mkulesh/stm32DevelopmentBoards/images/boards_bottom_view.jpg

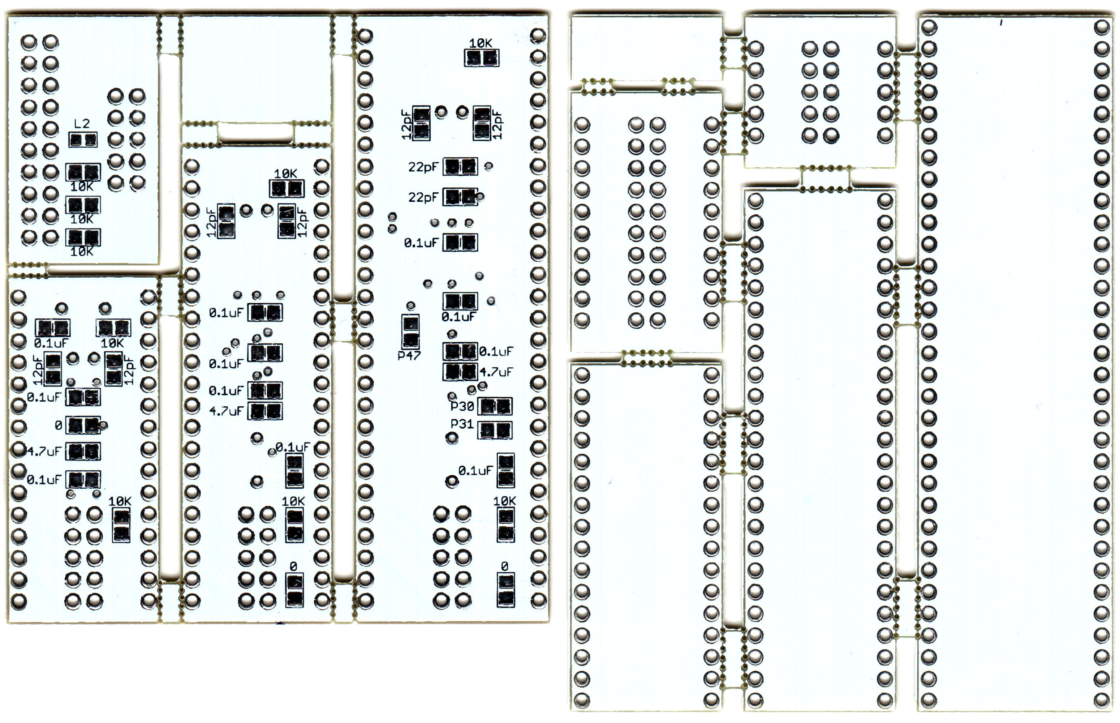
images/boards_bottom_view.jpg
