mkulesh/stm32DevelopmentBoards/images/boards_top_view.jpg

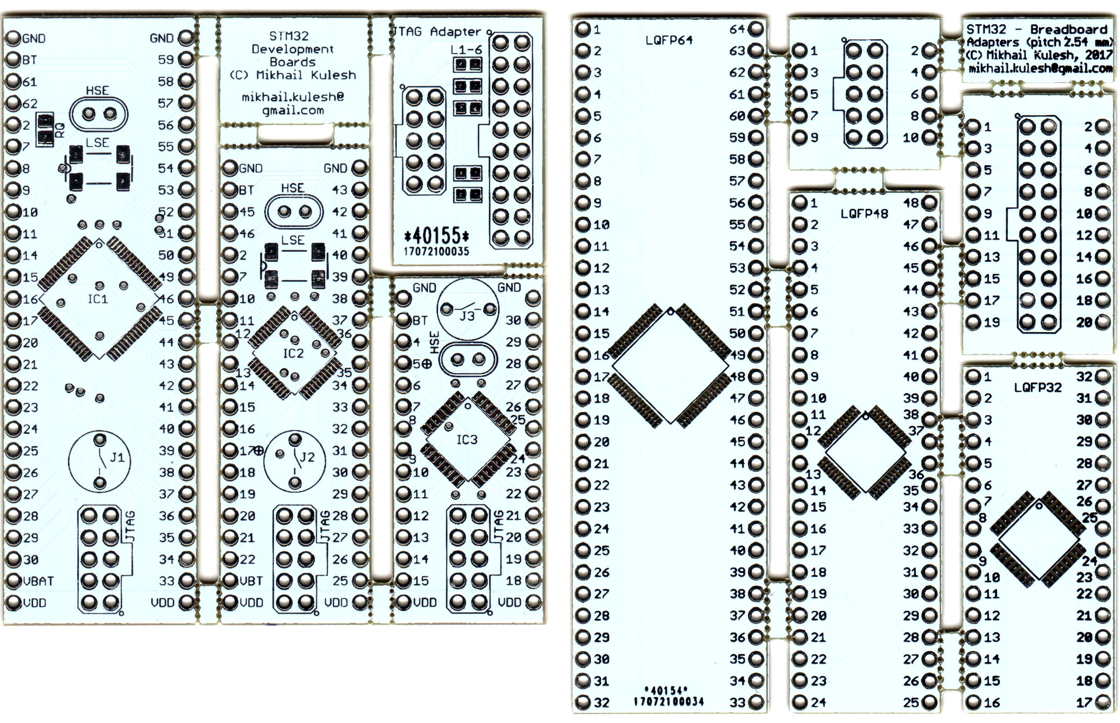
images/boards_top_view.jpg
