mkulesh/stm32DevelopmentBoards/images/F303K8_dev_board_jtag.jpg

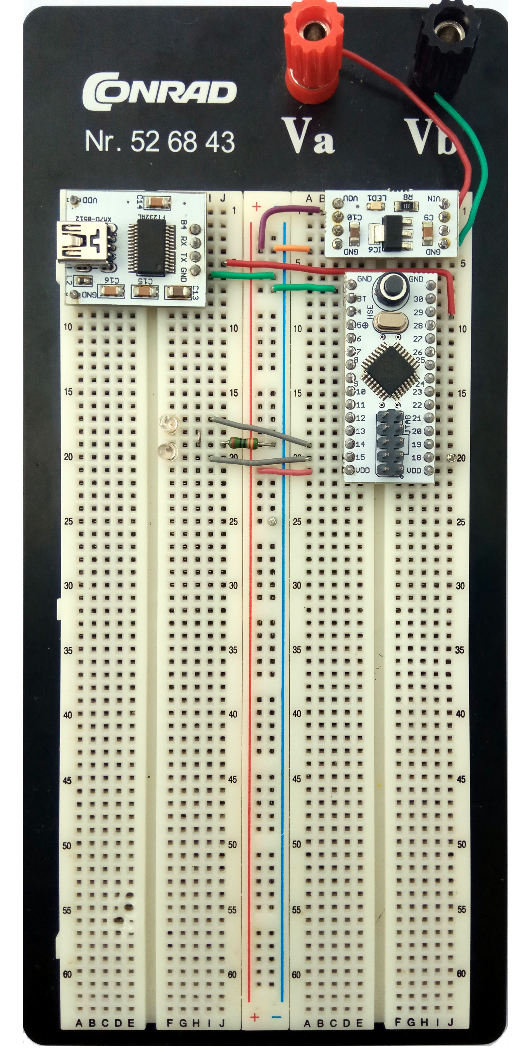
images/F303K8_dev_board_jtag.jpg
