mkulesh/stm32DevelopmentBoards/images/F373CB_adapter_board_jtag.jpg

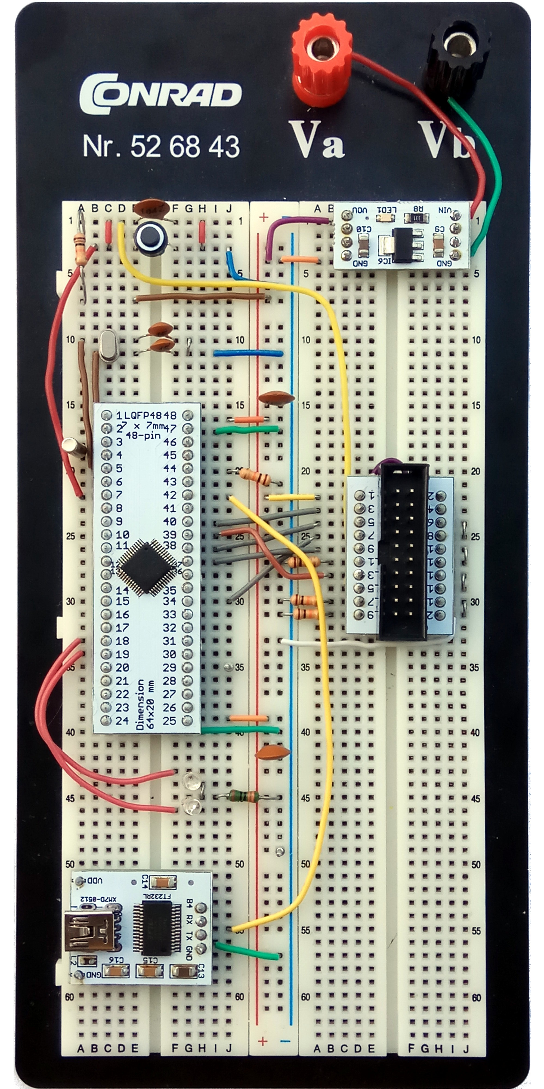
images/F373CB_adapter_board_jtag.jpg
