mkulesh/stm32DevelopmentBoards/images/F410RB_adapter_board_jtag.jpg

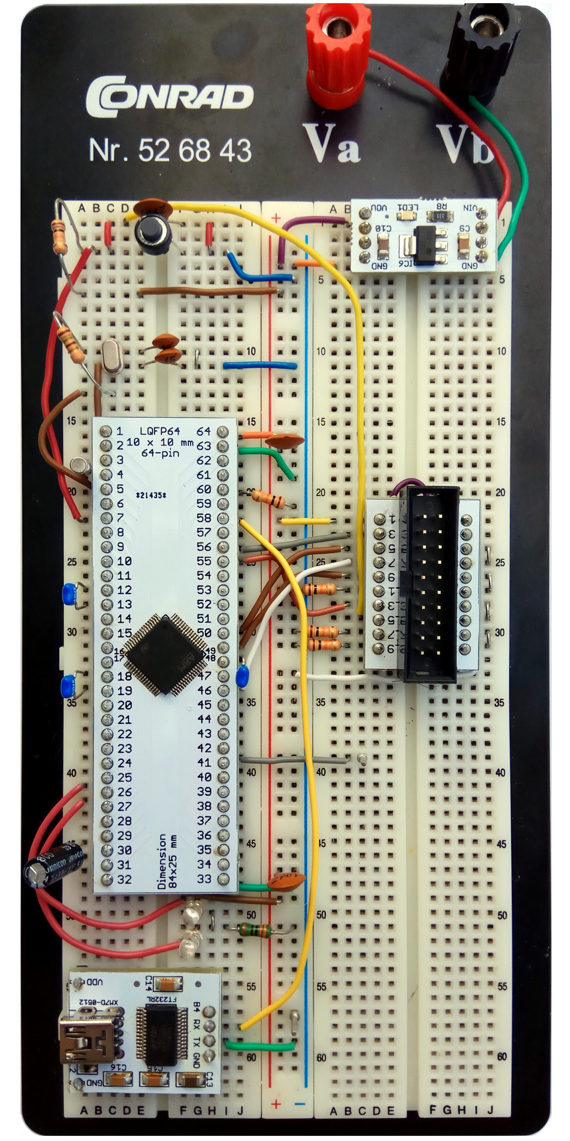
images/F410RB_adapter_board_jtag.jpg
