mkulesh/stm32DevelopmentBoards/images/F410RB_dev_board_jtag.jpg

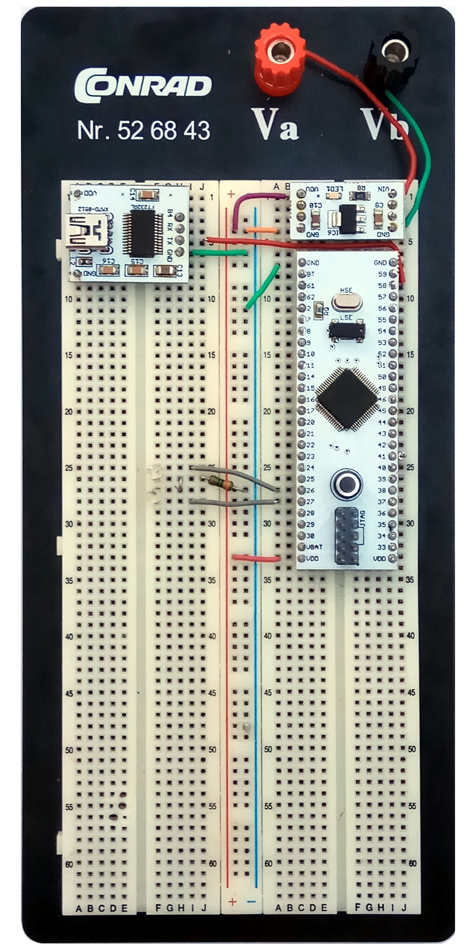
images/F410RB_dev_board_jtag.jpg
