mkulesh/stm32DevelopmentBoards/images/stm32pi-case.jpg

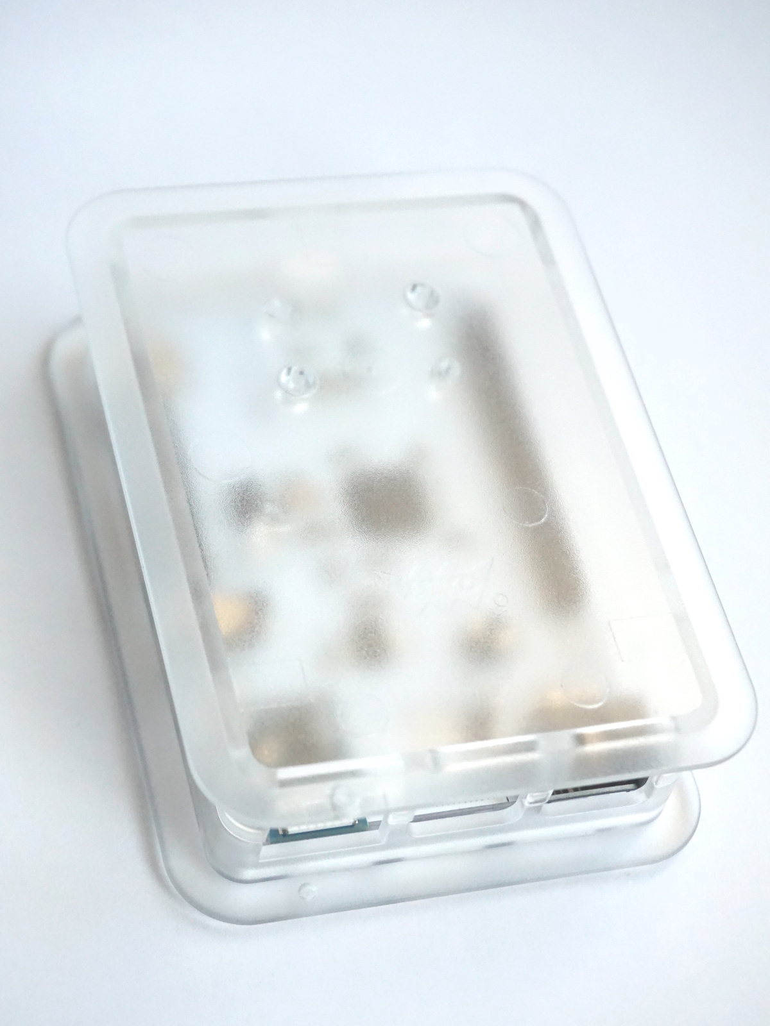
images/stm32pi-case.jpg
