mkulesh/stm32DevelopmentBoards/images/howToAssemble/assemble01.jpg

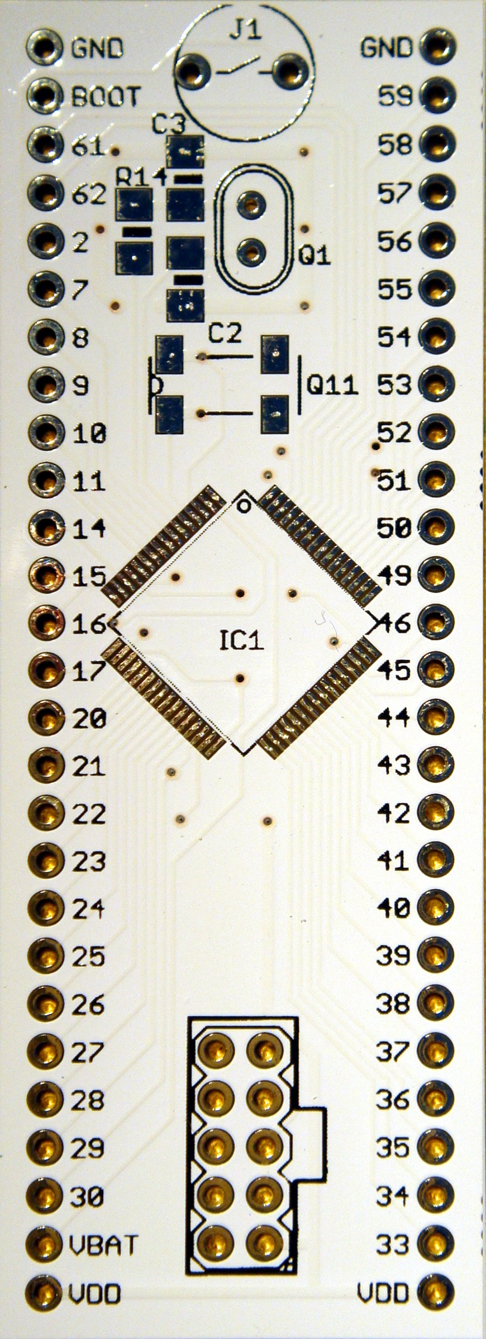
images/howToAssemble/assemble01.jpg
