mkulesh/stm32DevelopmentBoards/images/howToAssemble/assemble04.jpg

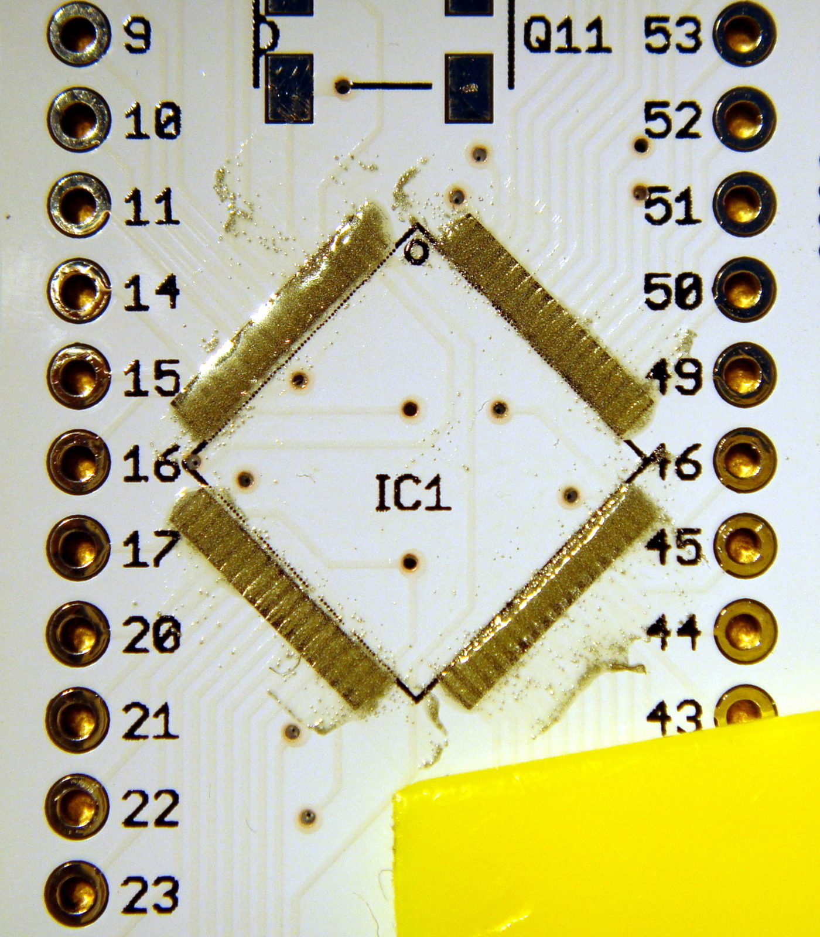
images/howToAssemble/assemble04.jpg
