mkulesh/stm32DevelopmentBoards/images/howToAssemble/assemble05.jpg

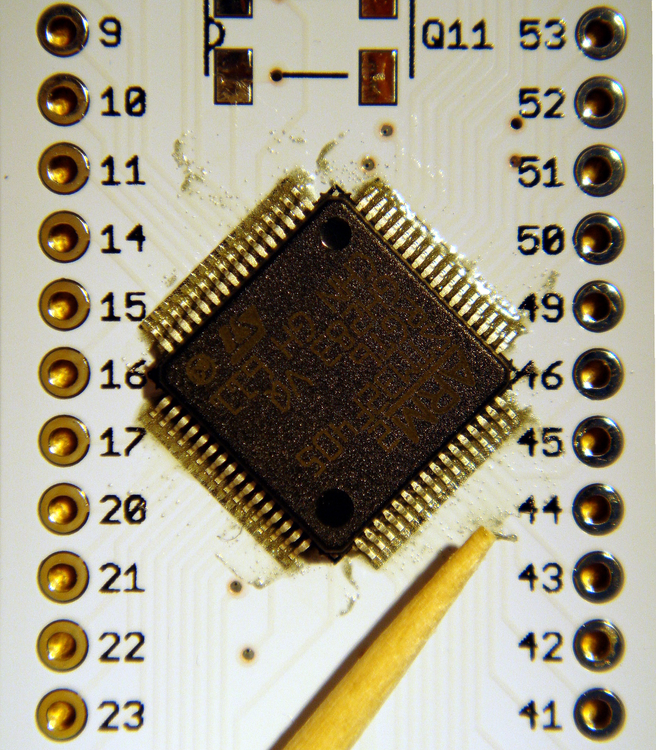
images/howToAssemble/assemble05.jpg
