mkulesh/stm32DevelopmentBoards/images/howToAssemble/assemble07.jpg

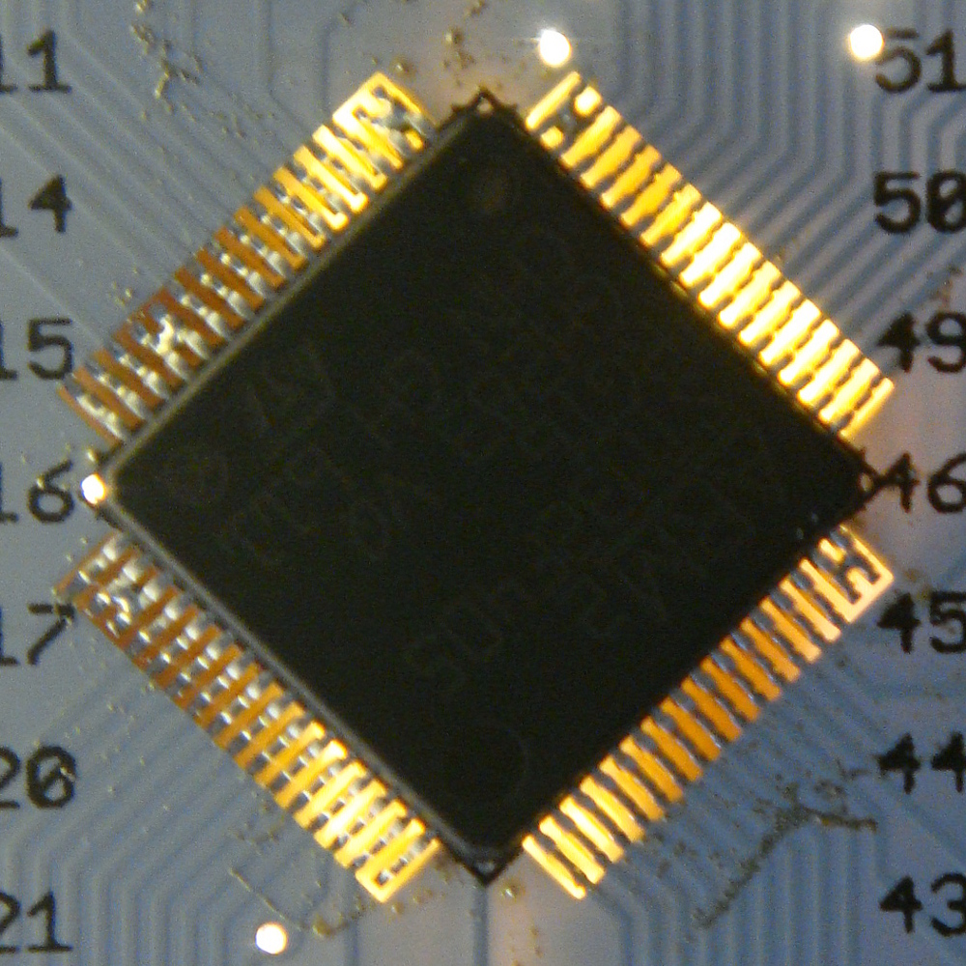
images/howToAssemble/assemble07.jpg
