mkulesh/stm32DevelopmentBoards/images/howToAssemble/assemble08.jpg

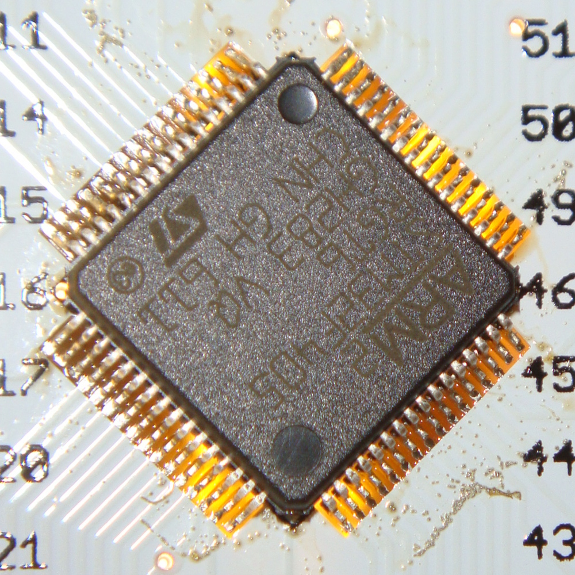
images/howToAssemble/assemble08.jpg
