mkulesh/stm32DevelopmentBoards/images/howToAssemble/assemble09.jpg

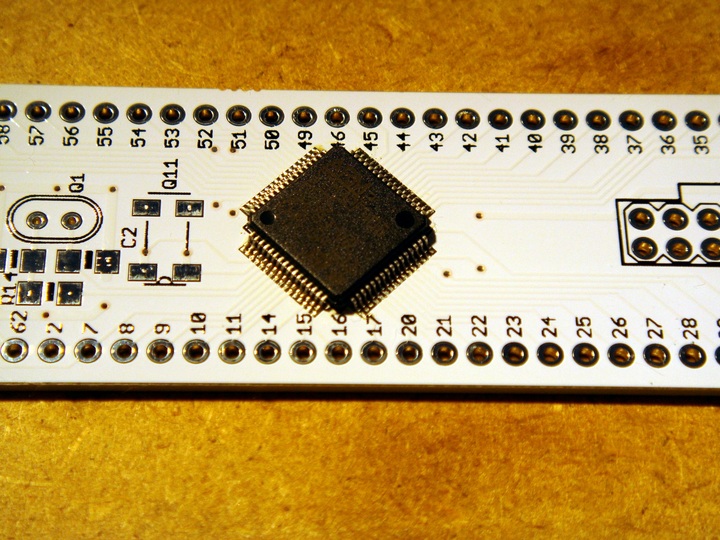
images/howToAssemble/assemble09.jpg
