mkulesh/stm32DevelopmentBoards/src/StmPlusPlus/StmPlusPlus.h

/*******************************************************************************
 * StmPlusPlus: object-oriented library implementing device drivers for 
 * STM32F3 and STM32F4 MCU
 * *****************************************************************************
 * Copyright (C) 2016-2017 Mikhail Kulesh
 * 
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
 * You should have received a copy of the GNU General Public License
 * along with this program.  If not, see <http://www.gnu.org/licenses/>.
 ******************************************************************************/

#ifndef STMPLUSPLUS_H_
#define STMPLUSPLUS_H_

// TODO:
// 1. Change all types to genetic types (aka int instead of in16_t)
// 2. Compile with maximal level of warning check
// 3. Compile with maximal optimization level

#include "HardwareLayout.h"

#include <ctime>
#include <cstring>
#include <cstdlib>
#include <functional>

namespace StmPlusPlus {

/**
 * @brief Additional time types and limits
 */
typedef int32_t duration_sec;
typedef uint64_t time_ms;
typedef int64_t duration_ms;

#define UNDEFINED_PRIO __UINT32_MAX__
#define INFINITY_SEC __UINT32_MAX__
#define INFINITY_TIME __UINT64_MAX__
#define FIRST_CALENDAR_YEAR 1900
#define MILLIS_IN_SEC 1000L

/**
 * @brief Useful primitives
 */
#define lowByte(x)                        ((uint8_t)((x) & 0xFF))
#define highByte(x)                       ((uint8_t)(((x)>>8) & 0xFF))
#define setBitToTrue(uInt8Val, bitNr)   (uInt8Val |= (1 << bitNr))
#define setBitToFalse(uInt8Val, bitNr)  (uInt8Val &= ~(1 << bitNr))

typedef union
{
    uint16_t word;
    struct
    {
        uint8_t low;
        uint8_t high;
    } bytes;
} WordToBytes;


/**
 * @brief Static class collecting helper methods for general system settings.
 */
class System
{
public:

    System (HardwareLayout::Interrupt && sysTickIrq);

    inline void initInstance ()
    {
        instance = this;
    }

    static System * getInstance ()
    {
        return instance;
    }

    void initHSE (bool external);
    void initLSE (bool external);
    void initPLL (uint32_t PLLM, uint32_t PLLN, uint32_t PLLP, uint32_t PLLQ, uint32_t PLLR = 0);
    void initAHB (uint32_t AHBCLKDivider, uint32_t APB1CLKDivider, uint32_t APB2CLKDivider);
    void initRTC ();
    void initI2S (uint32_t PLLI2SN, uint32_t PLLI2SR);

    inline uint32_t getHSEFreq () const
    {
        return HSE_VALUE;
    }

    inline uint32_t getHSIFreq () const
    {
        return HSI_VALUE;
    }

    inline uint32_t getMcuFreq () const
    {
        return mcuFreq;
    }

    void start (uint32_t fLatency, int32_t msAdjustment = 0);

private:

    static System * instance;
    RCC_OscInitTypeDef RCC_OscInitStruct;
    RCC_ClkInitTypeDef RCC_ClkInitStruct;
    RCC_PeriphCLKInitTypeDef PeriphClkInit;
    HardwareLayout::Interrupt sysTickIrq;
    uint32_t mcuFreq;
};


/**
 * @brief Base IO port class.
 */
class IOPort
{
public:

    /**
     * @brief Enumeration collecting port names.
     *
     * The port name will be used in the constructor in order to set-up the pointers to the port
     * registers.
     */
    enum PortName
    {
        A = 0,
        B = 1,
        C = 2,
        D = 3,
        F = 4
    };

    /**
     * @brief Default constructor.
     */
    IOPort (PortName name,
            uint32_t mode,
            uint32_t pull = GPIO_NOPULL,
            uint32_t speed = GPIO_SPEED_HIGH,
            uint32_t pin = GPIO_PIN_All,
            bool callInit = true);

    /**
     * @brief Default constructor.
     */
    IOPort (const HardwareLayout::Pins & device,
            uint32_t mode,
            uint32_t pull = GPIO_NOPULL,
            uint32_t speed = GPIO_SPEED_HIGH,
            bool callInit = true);

    /**
     * @brief Specifies the operating mode for the selected pins.
     */
    inline void setMode (uint32_t mode)
    {
        gpioParameters.Mode  = mode;
        HAL_GPIO_Init(port, &gpioParameters);
    }

    /**
     * @brief Specifies the Pull-up or Pull-Down activation for the selected pins.
     */
    inline void setPull (uint32_t pull)
    {
        gpioParameters.Pull  = pull;
        HAL_GPIO_Init(port, &gpioParameters);
    }

    /**
     * @brief Specifies the speed for the selected pins.
     */
    inline void setSpeed (uint32_t speed)
    {
        gpioParameters.Speed  = speed;
        HAL_GPIO_Init(port, &gpioParameters);
    }

    /**
     * @brief Peripheral to be connected to the selected pins.
     */
    inline void setAlternate (uint32_t alternate)
    {
        gpioParameters.Alternate  = alternate;
        HAL_GPIO_Init(port, &gpioParameters);
    }

    /**
     * @brief Lock GPIO Pins configuration registers.
     */
    inline void lock ()
    {
        HAL_GPIO_LockPin(port, gpioParameters.Pin);
    }

    /**
     * @brief  Set the selected data port bit.
     *
     * @note   This function uses GPIOx_BSRR and GPIOx_BRR registers to allow atomic read/modify
     *         accesses. In this way, there is no risk of an IRQ occurring between
     *         the read and the modify access.
     */
    inline void setHigh ()
    {
        HAL_GPIO_WritePin(port, gpioParameters.Pin, GPIO_PIN_SET);
    }

    /**
     * @brief  Clear the selected data port bit.
     *
     * @note   This function uses GPIOx_BSRR and GPIOx_BRR registers to allow atomic read/modify
     *         accesses. In this way, there is no risk of an IRQ occurring between
     *         the read and the modify access.
     */
    inline void setLow ()
    {
        HAL_GPIO_WritePin(port, gpioParameters.Pin, GPIO_PIN_RESET);
    }

    /**
     * @brief Toggle the specified GPIO pin.
     */
    inline void toggle ()
    {
        HAL_GPIO_TogglePin(port, gpioParameters.Pin);
    }

    /**
     * @brief Write the given integer into the GPIO port output data register.
     */
    inline void putInt (uint32_t val)
    {
        port->ODR = val;
    }

    /**
     * @brief Returns the value from GPIO port input data register.
     */
    inline uint32_t getInt ()
    {
        return port->IDR;
    }

protected:

    /**
     * @brief Pointer to the port registers.
     */
    GPIO_TypeDef * port;

    /**
     * @brief Current port parameters.
     */
    GPIO_InitTypeDef gpioParameters;
};


/**
 * @brief Class that describes a single port pin.
 */
class IOPin : public IOPort
{
public:

    /**
     * @brief Default constructor.
     */
    IOPin (PortName name, uint32_t pin, uint32_t mode, uint32_t pull = GPIO_NOPULL, uint32_t speed = GPIO_SPEED_HIGH, bool callInit = true, bool value = false):
        IOPort(name, mode, pull, speed, pin, callInit)
    {
        HAL_GPIO_WritePin(port, gpioParameters.Pin, (GPIO_PinState)value);
    }

    /**
     * @brief Default constructor.
     */
    IOPin (const HardwareLayout::Pins & device, uint32_t mode, uint32_t pull = GPIO_NOPULL, uint32_t speed = GPIO_SPEED_HIGH, bool callInit = true, bool value = false):
        IOPort(device, mode, pull, speed, callInit)
    {
        HAL_GPIO_WritePin(port, gpioParameters.Pin, (GPIO_PinState)value);
    }

    /**
     * @brief Set or clear the selected data port bit.
     *
     * @note   This function uses GPIOx_BSRR and GPIOx_BRR registers to allow atomic read/modify
     *         accesses. In this way, there is no risk of an IRQ occurring between
     *         the read and the modify access.
     */
    inline void putBit (bool value)
    {
        HAL_GPIO_WritePin(port, gpioParameters.Pin, (GPIO_PinState)value);
    }

    /**
     * @brief Return the current value of the pin.
     */
    inline bool getBit () const
    {
        return (bool)HAL_GPIO_ReadPin(port, gpioParameters.Pin);
    }

    /**
     * @brief Activate microcontroller clock output (MCO) for this pin.
     */
    void activateClockOutput (uint32_t source, uint32_t div = RCC_MCODIV_1);
};


/**
 * @brief Class that implements UART interface.
 */
class Usart
{
public:

    /**
     * @brief Default constructor.
     */
    Usart (const HardwareLayout::Usart * _device);

    /**
     * @brief Open transmission session with given parameters.
     */
    HAL_StatusTypeDef start (uint32_t mode,
                             uint32_t baudRate,
                             uint32_t wordLength = UART_WORDLENGTH_8B,
                             uint32_t stopBits = UART_STOPBITS_1,
                             uint32_t parity = UART_PARITY_NONE);

    /**
     * @brief Close the transmission session.
     */
    void stop ();

    /**
     * @brief Open transmission session with given mode.
     */
    inline HAL_StatusTypeDef startMode (uint32_t mode)
    {
        usartParameters.Init.Mode = mode;
        return HAL_UART_Init(&usartParameters);
    }

    /**
     * @brief Send an amount of data in blocking mode.
     */
    inline HAL_StatusTypeDef transmit (const char * buffer, size_t n, uint32_t timeout)
    {
        return HAL_UART_Transmit(&usartParameters, (unsigned char *)buffer, n, timeout);
    }

    inline HAL_StatusTypeDef transmit (const char * buffer)
    {
        return HAL_UART_Transmit(&usartParameters, (unsigned char *)buffer, ::strlen(buffer), 0xFFFF);
    }

    /**
     * @brief Receive an amount of data in blocking mode.
     */
    inline HAL_StatusTypeDef receive (const char * buffer, size_t n, uint32_t timeout)
    {
        return HAL_UART_Receive(&usartParameters, (unsigned char *)buffer, n, timeout);
    }

    /**
     * @brief Send an amount of data in interrupt mode.
     */
    inline HAL_StatusTypeDef transmitIt (const char * buffer, size_t n)
    {
        irqStatus = RESET;
        return HAL_UART_Transmit_IT(&usartParameters, (unsigned char *)buffer, n);
    }

    /**
     * @brief Receive an amount of data in interrupt mode.
     */
    inline HAL_StatusTypeDef receiveIt (const char * buffer, size_t n)
    {
        irqStatus = RESET;
        return HAL_UART_Receive_IT(&usartParameters, (unsigned char *)buffer, n);
    }

    /**
     * @brief Interrupt handling.
     */
    inline void startInterrupt ()
    {
        device->txRxIrq.start();
    }

    inline void stopInterrupt ()
    {
        device->txRxIrq.stop();
    }

    inline void processInterrupt ()
    {
        HAL_UART_IRQHandler(&usartParameters);
    }

    inline void processRxTxCpltCallback ()
    {
        irqStatus = SET;
    }

    inline bool isFinished () const
    {
        return irqStatus == SET;
    }

protected:

    const HardwareLayout::Usart * device;
    IOPin txPin, rxPin;
    UART_HandleTypeDef usartParameters;
    __IO ITStatus irqStatus;
};


#define IS_USART_DEBUG_ACTIVE() (UsartLogger::getInstance() != NULL)

#define USART_DEBUG(text) {\
    if (IS_USART_DEBUG_ACTIVE())\
    {\
        UsartLogger::getStream() << USART_DEBUG_MODULE << text << UsartLogger::ENDL;\
    }}


/**
 * @brief Class implementing USART logger.
 */
class UsartLogger : public Usart
{
public:

    const uint32_t TIMEOUT = 1000;

    enum Manupulator
    {
        ENDL = 0
    };

    /**
     * @brief Default constructor.
     */
    UsartLogger (const HardwareLayout::Usart * _device, uint32_t _baudRate);

    void initInstance ();

    static UsartLogger * getInstance ()
    {
        return instance;
    }

    static UsartLogger & getStream ()
    {
        return *instance;
    }

    inline void clearInstance ()
    {
        stop();
        instance = NULL;
    }

    UsartLogger & operator << (const char * buffer);

    UsartLogger & operator << (int n);

    UsartLogger & operator << (Manupulator m);

private:

    static UsartLogger * instance;
    uint32_t baudRate;

    void waitForRelease ();
};


/**
 * @brief Class that implements basic timer interface.
 */
class TimerBase
{
public:

    /**
     * @brief Default constructor.
     */
    TimerBase (const HardwareLayout::Timer * _device);

    inline TIM_HandleTypeDef * getTimerParameters ()
    {
        return &timerParameters;
    }

    HAL_StatusTypeDef startCounter (uint32_t counterMode,
                             uint32_t prescaler,
                             uint32_t period,
                             uint32_t clockDivision = TIM_CLOCKDIVISION_DIV1);

    inline HAL_StatusTypeDef startCounterInMillis ()
    {
        // TODO: here, there is some problem related to SystemCoreClock frequency
        return startCounter(TIM_COUNTERMODE_UP, SystemCoreClock/4000 - 1, __UINT32_MAX__, TIM_CLOCKDIVISION_DIV1);
    }

    void stopCounter ();

    inline uint32_t getValue () const
    {
        return __HAL_TIM_GET_COUNTER(&timerParameters);
    }

    inline void reset ()
    {
        __HAL_TIM_SET_COUNTER(&timerParameters, 0);
    }

protected:

    const HardwareLayout::Timer * device;
    TIM_HandleTypeDef timerParameters;
};


/**
 * @brief Class that implements PWM based on a timer.
 */
class PulseWidthModulation : public TimerBase
{
public:

    PulseWidthModulation (const HardwareLayout::Timer * _device, IOPort::PortName name, uint32_t _pin, uint32_t channel);

    bool start (uint32_t freq);
    void stop ();

private:

    IOPin pin;
    uint32_t channel;
    TIM_OC_InitTypeDef channelParameters;
};


/**
 * @brief Class that implements timer interface.
 */
class Timer : public TimerBase
{
public:

    class EventHandler
    {
    public:

        virtual void onTimerUpdate (const Timer *) =0;
    };

    /**
     * @brief Default constructor.
     */
    Timer (const HardwareLayout::Timer * _device);

    inline void setHandler (EventHandler * _handler)
    {
        handler = _handler;
    }

    void setPrescaler (uint32_t prescaler);
    void setPeriod (uint32_t period);

    HAL_StatusTypeDef start (uint32_t counterMode,
                             uint32_t prescaler,
                             uint32_t period,
                             uint32_t clockDivision = TIM_CLOCKDIVISION_DIV1,
                             uint32_t repetitionCounter = 1);

    void processInterrupt () const;

    void stop ();

private:

    EventHandler * handler;
};


/**
 * @brief Class that implements real-time clock.
 */
class RealTimeClock
{
public:

    class EventHandler
    {
    public:

        virtual void onRtcWakeUp () =0;
    };

    // NTP Message
    static const size_t NTP_PACKET_SIZE = 48;  // NTP time is in the first 48 bytes of message
    struct NtpPacket {
            uint8_t flags;
            uint8_t stratum;
            uint8_t poll;
            uint8_t precision;
            uint32_t root_delay;
            uint32_t root_dispersion;
            uint8_t referenceID[4];
            uint32_t ref_ts_sec;
            uint32_t ref_ts_frac;
            uint32_t origin_ts_sec;
            uint32_t origin_ts_frac;
            uint32_t recv_ts_sec;
            uint32_t recv_ts_frac;
            uint32_t trans_ts_sec;
            uint32_t trans_ts_frac;
    } __attribute__((__packed__));

    /**
     * @brief Default constructor.
     */
    RealTimeClock (const HardwareLayout::Rtc * _device);

    inline void initInstance ()
    {
        instance = this;
    }

    static RealTimeClock * getInstance ()
    {
        return instance;
    }

    inline time_ms getUpTimeMillisec () const
    {
        return upTimeMillisec;
    }

    inline time_t getTimeSec () const
    {
        return timeSec;
    }

    void setTimeSec (time_t sec)
    {
        timeSec = sec;
    }

    HAL_StatusTypeDef start (uint32_t counterMode, uint32_t prescaler, RealTimeClock::EventHandler * _handler = NULL);

    void onMilliSecondInterrupt ();
    void onSecondInterrupt ();

    void stop ();
    const char * getLocalTime ();
    void fillNtpRrequst (NtpPacket & ntpPacket);
    void decodeNtpMessage (NtpPacket & ntpPacket);

private:

    static RealTimeClock * instance;
    const HardwareLayout::Rtc * device;
    EventHandler * handler;
    RTC_HandleTypeDef rtcParameters;
    RTC_TimeTypeDef timeParameters;
    RTC_DateTypeDef dateParameters;

    // These variables are modified from interrupt service routine, therefore declare them as volatile
    volatile time_ms upTimeMillisec; // up time (in milliseconds)
    volatile time_t timeSec; // up-time and current time (in seconds)
    char localTime[24];
};


class DeviceClient
{
public:

    virtual ~DeviceClient ()
    {
        // empty
    }

    virtual bool onTransmissionFinished () =0;
};


class SharedDevice
{
public:

    const uint32_t TIMEOUT = 1000;

    SharedDevice () : client{NULL}
    {
        // empty
    }

    inline bool isUsed () const
    {
        return client != NULL;
    }

    inline void processDmaTxInterrupt ()
    {
        HAL_DMA_IRQHandler(&txDma);
    }

    inline void processTxCpltCallback ()
    {
        if (client != NULL && client->onTransmissionFinished())
        {
            client = NULL;
        }
    }

    inline void processDmaRxInterrupt ()
    {
        HAL_DMA_IRQHandler(&rxDma);
    }

    inline void processRxCpltCallback ()
    {
        if (client != NULL && client->onTransmissionFinished())
        {
            client = NULL;
        }
    }

    void waitForRelease ();

protected:

    DeviceClient * client;
    DMA_HandleTypeDef txDma;
    DMA_HandleTypeDef rxDma;
};


/**
 * @brief Class that implements SPI interface.
 */
class Spi : public SharedDevice
{
public:

    /**
     * @brief Default constructor.
     */
    Spi (const HardwareLayout::Spi * _device, uint32_t pull = GPIO_NOPULL);

    HAL_StatusTypeDef start (uint32_t direction, uint32_t prescaler, uint32_t dataSize = SPI_DATASIZE_8BIT, uint32_t CLKPhase = SPI_PHASE_1EDGE);

    void stop ();

    /**
     * @brief Send an amount of data in blocking mode.
     */
    inline void putChar (uint8_t data)
    {
        /* Transmit data in 8 Bit mode */
        spiParams.Instance->DR = data;
        while (!__HAL_SPI_GET_FLAG(&spiParams, SPI_FLAG_TXE));
    }

    inline void putInt (uint16_t data)
    {
        /* Transmit data in 16 Bit mode */
        spiParams.Instance->DR = data;
        while (!__HAL_SPI_GET_FLAG(&spiParams, SPI_FLAG_TXE));
    }

    inline HAL_StatusTypeDef transmit (uint8_t *pData, uint16_t pSize)
    {
        return HAL_SPI_Transmit(&spiParams, pData, pSize, TIMEOUT);
    }

    /**
     * @brief Send an amount of data in interrupt mode.
     */
    inline HAL_StatusTypeDef transmitDma (DeviceClient * _client, uint8_t *buffer, size_t n)
    {
        client = _client;
        return HAL_SPI_Transmit_DMA(&spiParams, buffer, n);
    }

    inline bool isBusy () const
    {
        return (((spiParams.Instance->SR) & (SPI_FLAG_BSY)) == (SPI_FLAG_BSY));
    }

private:

    const HardwareLayout::Spi * device;
    IOPort pins;
    SPI_HandleTypeDef spiParams;
};


/**
 * @brief Class that implements a periodical event with a given delay
 */
class PeriodicalEvent
{
private:

    time_ms lastEventTime, delay;
    long maxOccurrence, occurred;

public:

    PeriodicalEvent (time_ms _delay, long _maxOccurrence = -1);
    void resetTime ();
    bool isOccured ();
    inline long occurance () const
    {
        return occurred;
    }
};


/**
 * @brief Class that implements analog-to-digit converter
 */
class AnalogToDigitConverter : public SharedDevice
{
public:

    const uint32_t INVALID_VALUE = __UINT32_MAX__;
    static const size_t ADC_BUFFER_LENGTH = 100;

    AnalogToDigitConverter (const HardwareLayout::Adc * _device, uint32_t channel, uint32_t samplingTime, float _vRef);

    HAL_StatusTypeDef start ();
    void stop ();
    
    float read ();
    HAL_StatusTypeDef readDma ();
    
    inline float getVoltage ()
    {
        return vMeasured;
    }

    inline int getMV ()
    {
        return (int)(vMeasured * 1000);
    }

    bool processConvCpltCallback ();

private:

    const HardwareLayout::Adc * device;
    IOPin pin;
    ADC_HandleTypeDef adcParams;
    ADC_ChannelConfTypeDef adcChannel;
    float vRef, vMeasured;
    size_t nrReadings;
    std::array<uint32_t, ADC_BUFFER_LENGTH> adcBuffer;
};


/**
 * @brief Class that implements I2S interface
 */
class I2S : public SharedDevice
{
public:

    I2S (const HardwareLayout::I2S * _device);
    HAL_StatusTypeDef start (uint32_t standard, uint32_t audioFreq, uint32_t dataFormat);
    void stop ();

    inline HAL_StatusTypeDef transmitDma (DeviceClient * _client, uint16_t * pData, uint16_t size)
    {
        client = _client;
        return HAL_I2S_Transmit_DMA(&i2s, pData, size);
    }

private:

    const HardwareLayout::I2S * device;
    IOPort pins;
    I2S_HandleTypeDef i2s;
};

} // end namespace
#endif
