mkulesh/stm32DevelopmentBoards/src/StmPlusPlus/Devices/Esp11.h

/*******************************************************************************
 * StmPlusPlus: object-oriented library implementing device drivers for
 * STM32F3 and STM32F4 MCU
 * *****************************************************************************
 * Copyright (C) 2016-2017 Mikhail Kulesh
 *
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
 * You should have received a copy of the GNU General Public License
 * along with this program.  If not, see <http://www.gnu.org/licenses/>.
 ******************************************************************************/

#ifndef ESP11_H_
#define ESP11_H_

#include "StmPlusPlus/StmPlusPlus.h"

namespace StmPlusPlus
{
namespace Devices
{

/************************************************************************
 * Class Esp11
 ************************************************************************/

class Esp11
{
public:
    
    enum class AsyncCmd
    {
        POWER_ON       = 0,
        ECHO_OFF       = 1,
        ENSURE_READY   = 2,
        SET_MODE       = 3,
        ENSURE_MODE    = 4,
        SET_ADDR       = 5,
        ENSURE_WLAN    = 6,
        CONNECT_WLAN   = 7,
        PING_SERVER    = 8,
        SET_CON_MODE   = 9,
        SET_SINDLE_CON = 10,
        CONNECT_SERVER = 11,
        SEND_MSG_SIZE  = 12,
        SEND_MESSAGE   = 13,
        RECONNECT      = 14,
        DISCONNECT     = 15,
        POWER_OFF      = 16,
        WAITING        = 17,
        OFF            = 18
    };

    enum class CommState
    {
        NONE    = 0,
        TX      = 1,
        TX_CMPL = 2,
        RX      = 3,
        SUCC    = 4,
        ERROR   = 5
    };

    static const uint32_t ESP_BAUDRATE = 115200;
    static const time_ms ESP_TIMEOUT = 30000L;
    static const uint32_t BUFFER_SIZE = 1024;

public:
    
    Esp11 (const HardwareLayout::Usart * usartDevice, IOPort::PortName powerPort, uint32_t powerPin);

    inline void processRxCpltCallback ()
    {
        commState = CommState::ERROR;
    }

    inline void processTxCpltCallback ()
    {
        commState = CommState::TX_CMPL;
    }
    
    inline void processErrorCallback ()
    {
        commState = CommState::ERROR;
    }

    inline void processInterrupt ()
    {
        usart.processInterrupt();
        if (commState == CommState::TX_CMPL)
        {
            commState = CommState::RX;
            rxIndex = 0;
            usart.startMode(UART_MODE_RX);
            usart.receiveIt(rxBuffer, BUFFER_SIZE);
        }
        else if (commState == CommState::RX && rxIndex < BUFFER_SIZE)
        {
            if (rxIndex >= 1
                && rxBuffer[rxIndex-1] == '\r'
                && rxBuffer[rxIndex] == '\n')
            {
                if (shortOkResponse && rxIndex >= 3
                    && rxBuffer[rxIndex - 3] == 'O'
                    && rxBuffer[rxIndex - 2] == 'K')
                {
                    commState = CommState::SUCC;
                }
                else if (rxIndex >= 8
                        && rxBuffer[rxIndex - 8] == 'S'
                        && rxBuffer[rxIndex - 7] == 'E'
                        && rxBuffer[rxIndex - 6] == 'N'
                        && rxBuffer[rxIndex - 5] == 'D'
                        && rxBuffer[rxIndex - 4] == ' '
                        && rxBuffer[rxIndex - 3] == 'O'
                        && rxBuffer[rxIndex - 2] == 'K')
                {
                    commState = CommState::SUCC;
                }
                else if (rxIndex >= 6
                        && rxBuffer[rxIndex - 6] == 'E'
                        && rxBuffer[rxIndex - 5] == 'R'
                        && rxBuffer[rxIndex - 4] == 'R'
                        && rxBuffer[rxIndex - 3] == 'O'
                        && rxBuffer[rxIndex - 2] == 'R')
                {
                    commState = CommState::ERROR;
                }
            }
            ++rxIndex;
            if (commState == CommState::SUCC)
            {
                startListening();
            }
        }
        else if (listening && rxIndex < BUFFER_SIZE)
        {
            ++rxIndex;
        }
    }
    
    inline void setMode (int mode)
    {
        this->mode = mode;
    }

    inline void setIp (const char* ip)
    {
        this->ip = ip;
    }

    inline void setMask (const char* mask)
    {
        this->mask = mask;
    }

    inline void setGatway (const char* gatway)
    {
        this->gatway = gatway;
    }

    inline void setSsid (const char* ssid)
    {
        this->ssid = ssid;
    }

    inline void setPasswd (const char* passwd)
    {
        this->passwd = passwd;
    }

    inline void setProtocol (const char* protocol)
    {
        this->protocol = protocol;
    }

    inline void setServer (const char* server)
    {
        this->server = server;
    }

    inline void setPort (const char* port)
    {
        this->port = port;
    }

    inline void setMessage (const char* message)
    {
        this->message = message;
    }

    inline void setMessageSize (size_t messageSize)
    {
        this->messageSize = messageSize;
    }

    inline void assignSendLed (IOPin * _sendLed)
    {
        sendLed = _sendLed;
    }
    
    inline bool isResponceAvailable ()
    {
        return commState == CommState::SUCC || commState == CommState::ERROR;
    }

    inline bool isTransmissionStarted ()
    {
        return commState != CommState::NONE;
    }

    inline size_t getInputMessageSize () const
    {
        return inputMessageSize;
    }

    inline bool isListening ()
    {
        return listening;
    }
    
    inline const char* getProtocol () const
    {
        return protocol;
    }
    
    inline const char* getServer () const
    {
        return server;
    }

    inline const char* getPort () const
    {
        return port;
    }
    
    bool transmit (AsyncCmd cmd);
    bool getResponce (AsyncCmd cmd);
    void periodic ();
    void getInputMessage (char * buffer, size_t len);

private:

    const char * CMD_AT = "AT";
    const char * CMD_VERSION = "AT+GMR";
    const char * CMD_ECHO_OFF = "ATE0";
    const char * CMD_ECHO_ON = "ATE1";
    const char * CMD_GETMODE = "AT+CWMODE?";
    const char * CMD_SETMODE = "AT+CWMODE=";
    const char * RESP_GETMODE = "+CWMODE:";
    const char * CMD_SETIP = "AT+CIPSTA_CUR=";
    const char * CMD_GETIP = "AT+CIFSR";
    const char * CMD_GETNET = "AT+CWLAP=";
    const char * RESP_GETNET = "+CWLAP:";
    const char * CMD_CONNECT_WLAN = "AT+CWJAP_CUR=";
    const char * CMD_PING = "AT+PING=";
    const char * CMD_MULTCON = "AT+CIPMUX=1";
    const char * CMD_TCPSERVER = "AT+CIPSERVER=1,";
    const char * CMD_SET_NORMAL_MODE = "AT+CIPMODE=0";
    const char * CMD_SET_SINGLE_CONNECTION = "AT+CIPMUX=0";
    const char * CMD_CONNECT_SERVER = "AT+CIPSTART=";
    const char * CMD_CONNECT_SERVER_RESPONCE = "CONNECT";
    const char * CMD_SEND = "AT+CIPSEND=";
    const char * CMD_CLOSE_CONNECT = "AT+CIPCLOSE";
    const char * CMD_INPUT_MESSAGE = "+IPD,";
    const char * CMD_END = "\r\n";
    const char * RESP_READY = "ready\r\n";
    const char * UDP_PORT = "5888,0";

    Usart usart;
    IOPin pinPower;
    IOPin * sendLed;

    __IO CommState commState;
    __IO size_t rxIndex;
    __IO bool listening;
    __IO bool shortOkResponse;

    int mode;
    const char * ip;
    const char * gatway;
    const char * mask;
    const char * ssid;
    const char * passwd;
    const char * protocol;
    const char * server;
    const char * port;
    const char * message;
    size_t messageSize;
    time_ms operationEnd;
    const char * inputMessage;
    size_t inputMessageSize;

    char cmdBuffer[256];
    char txBuffer[BUFFER_SIZE];
    char rxBuffer[BUFFER_SIZE];
    char msgBuffer[BUFFER_SIZE];

    bool waitForResponce (const char * responce);
    bool sendCmd (const char * cmd, size_t cmdLen = 0, bool addCmdEnd = true);
    bool init ();
    bool applyMode ();
    bool applyIpAddress ();
    bool searchWlan ();
    bool connectToWlan ();
    bool ping ();
    bool connectToServer ();
    bool sendMessageSize ();
    bool sendMessage ();
    void processInputMessage ();
    void startListening ();
    void stopListening ();

    inline void powerOff ()
    {
        usart.stopInterrupt();
        usart.stop();
        pinPower.putBit(false);
    }

    inline void setInputMessage (const char * msg, size_t len)
    {
        inputMessage = msg;
        inputMessageSize = len;
    }
};

} // end of namespace Devices
} // end of namespace StmPlusPlus

#endif
