mkulesh/stm32DevelopmentBoards/src/StmPlusPlus/Devices/AudioDac_UDA1334.cpp

/*******************************************************************************
 * StmPlusPlus: object-oriented library implementing device drivers for 
 * STM32F3 and STM32F4 MCU
 * *****************************************************************************
 * Copyright (C) 2016-2017 Mikhail Kulesh
 * 
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
 * You should have received a copy of the GNU General Public License
 * along with this program.  If not, see <http://www.gnu.org/licenses/>.
 ******************************************************************************/

#include "AudioDac_UDA1334.h"

#include <cmath>
#define M_PI 3.14159265358979323846

using namespace StmPlusPlus;
using namespace StmPlusPlus::Devices;

#define USART_DEBUG_MODULE "DAC: "

AudioDac_UDA1334::AudioDac_UDA1334 (I2S & _i2s,
                                    IOPort::PortName powerPort, uint32_t powerPin,
                                    IOPort::PortName mutePort, uint32_t mutePin,
                                    IOPort::PortName smplFreqPort, uint32_t smplFreqPin) :
        i2s(_i2s),
        power(powerPort, powerPin, GPIO_MODE_OUTPUT_PP, GPIO_PULLDOWN, GPIO_SPEED_LOW, true, false),
        mute(mutePort, mutePin, GPIO_MODE_OUTPUT_PP, GPIO_PULLDOWN, GPIO_SPEED_LOW, true, false),
        smplFreq(smplFreqPort, smplFreqPin, GPIO_MODE_OUTPUT_PP, GPIO_PULLDOWN, GPIO_SPEED_LOW, true, false),
        sourceType(SourceType::STREAM),
        dataPtr1(NULL),
        dataPtr2(NULL),
        currDataBuffer(NULL),
        blockRequested(false),
        testPin(NULL)
{
    dataPtr1 = &dataBuffer1[0];
    dataPtr2 = &dataBuffer2[0];
}

bool AudioDac_UDA1334::start (AudioDac_UDA1334::SourceType s, uint32_t standard, uint32_t audioFreq,
                              uint32_t dataFormat)
{
    sourceType = s;
    currDataBuffer = NULL;
    blockRequested = false;
    
    switch (sourceType)
    {
    case SourceType::STREAM:
        ::memset(dataBuffer1, MSB_OFFSET, BLOCK_SIZE2);
        ::memset(dataBuffer2, MSB_OFFSET, BLOCK_SIZE2);
        // nothing to do
        break;
    case SourceType::TEST_LIN:
        makeTestSignalLin();
        break;
    case SourceType::TEST_SIN:
        makeTestSignalSin();
        break;
    }

    mute.putBit(true);
    power.putBit(true);
    if (START_DELAY > 0)
    {
        HAL_Delay(START_DELAY);
    }

    HAL_StatusTypeDef status = i2s.start(standard, audioFreq, dataFormat);
    USART_DEBUG("I2S start status: " << status);
    if (status != HAL_OK)
    {
        return false;
    }

    smplFreq.putBit(audioFreq > I2S_AUDIOFREQ_48K);
    currDataBuffer = dataPtr2;
    onTransmissionFinished();
    mute.putBit(false);
    
    return true;
}

void AudioDac_UDA1334::stop ()
{
    mute.putBit(false);
    smplFreq.putBit(false);
    power.putBit(false);
    i2s.stop();
    // do not clear sourceType
    currDataBuffer = NULL;
    blockRequested = false;
}

bool AudioDac_UDA1334::onTransmissionFinished ()
{
    if (currDataBuffer == NULL)
    {
        return true;
    }
    if (testPin != NULL)
    {
        testPin->putBit(!testPin->getBit());
    }
    HAL_StatusTypeDef status = HAL_ERROR;
    if (currDataBuffer == dataPtr1)
    {
        currDataBuffer = dataPtr2;
        status = i2s.transmitDma(this, dataPtr2, BLOCK_SIZE2);
    }
    else
    {
        currDataBuffer = dataPtr1;
        status = i2s.transmitDma(this, dataPtr1, BLOCK_SIZE2);
    }
    if (status != HAL_OK)
    {
        USART_DEBUG("I2S/DMA transmission error: " << status);
    }
    else
    {
        blockRequested = true;
    }
    return false;
}

void AudioDac_UDA1334::makeTestSignalLin ()
{
    uint16_t l, r;
    double maxValue = (double) 0xFFFF;
    double f = (double) (BLOCK_SIZE2);
    for (size_t i = 0; i < BLOCK_SIZE2; i += 2)
    {
        l = r = (uint16_t) (((double) i / f) * maxValue) + MSB_OFFSET;
        dataPtr1[i + 0] = l;
        dataPtr1[i + 1] = r;
        l = r = (uint16_t) ((1.0 - (double) i / f) * maxValue) + MSB_OFFSET;
        dataPtr2[i + 0] = l;
        dataPtr2[i + 1] = r;
    }
    USART_DEBUG("WAV streaming (LIN test signal) started...");
}

void AudioDac_UDA1334::makeTestSignalSin ()
{
    uint16_t l, r;
    double maxValue = (double) 0xFFFF;
    double f = (double) (BLOCK_SIZE2);
    for (size_t i = 0; i < BLOCK_SIZE2; i += 2)
    {
        l = (sin(2.0 * M_PI * (double) i / f) + 1.0) * maxValue / 2.0 + MSB_OFFSET;
        r = (cos(4.0 * M_PI * (double) i / f) + 1.0) * maxValue / 2.0 + MSB_OFFSET;
        dataPtr1[i + 0] = l;
        dataPtr1[i + 1] = r;
        dataPtr2[i + 0] = l;
        dataPtr2[i + 1] = r;
    }
    USART_DEBUG("WAV streaming (SIN test signal) started...");
}
