mkulesh/stm32DevelopmentBoards/src/StmPlusPlus/Devices/Ssd.cpp

/*******************************************************************************
 * StmPlusPlus: object-oriented library implementing device drivers for 
 * STM32F3 and STM32F4 MCU
 * *****************************************************************************
 * Copyright (C) 2016-2017 Mikhail Kulesh
 * 
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
 * You should have received a copy of the GNU General Public License
 * along with this program.  If not, see <http://www.gnu.org/licenses/>.
 ******************************************************************************/

#include "Ssd.h"

using namespace StmPlusPlus;
using namespace StmPlusPlus::Devices;

/************************************************************************
 * Class SegmentsMask
 ************************************************************************/
Ssd::SegmentsMask::SegmentsMask ()
{
    top = 0;
    rightTop = 1;
    rightBottom = 2;
    bottom = 3;
    leftBottom = 4;
    leftTop = 5;
    center = 6;
    dot = 7;
}

char Ssd::getBits (char c, bool dot) const
{
    char bits = 0;
    switch (c)
    {
        case '.':
            bits |= (1 << sm.dot);
            break;
        case '-':
            bits |= (1 << sm.center);
            break;
        case 0: case '0':
            bits = (1 << sm.top) | (1 << sm.rightTop) | (1 << sm.rightBottom)
            | (1 << sm.bottom) | (1 << sm.leftBottom) | (1 << sm.leftTop);
            break;
        case 1: case '1':
            bits = (1 << sm.rightTop) | (1 << sm.rightBottom);
            break;
        case 2: case '2':
            bits = (1 << sm.top) | (1 << sm.rightTop) | (1 << sm.center)
            | (1 << sm.leftBottom) | (1 << sm.bottom);
            break;
        case 3: case '3':
            bits = (1 << sm.top) | (1 << sm.rightTop) | (1 << sm.center)
            | (1 << sm.rightBottom) | (1 << sm.bottom);
            break;
        case 4: case '4':
            bits = (1 << sm.leftTop) | (1 << sm.center) | (1 << sm.rightTop)
            | (1 << sm.rightBottom);
            break;
        case 5: case '5':
            bits = (1 << sm.top) | (1 << sm.leftTop) | (1 << sm.center)
            | (1 << sm.rightBottom) | (1 << sm.bottom);
            break;
        case 6: case '6':
            bits = (1 << sm.top) | (1 << sm.leftTop) | (1 << sm.center)
            | (1 << sm.rightBottom) | (1 << sm.bottom) | (1 << sm.leftBottom);
            break;
        case 7: case '7':
            bits = (1 << sm.top) | (1 << sm.rightTop) | (1 << sm.rightBottom);
            break;
        case 8: case '8':
            bits = (1 << sm.top) | (1 << sm.rightTop) | (1 << sm.center)
            | (1 << sm.rightBottom) | (1 << sm.bottom) | (1 << sm.leftBottom) | (1 << sm.leftTop);
            break;
        case 9: case '9':
            bits = (1 << sm.top) | (1 << sm.rightTop) | (1 << sm.center)
            | (1 << sm.rightBottom) | (1 << sm.bottom) | (1 << sm.leftTop);
            break;
        default:
            break;
    }
    if (dot)
    {
        bits |= (1 << sm.dot);
    }
    return bits;
}



/************************************************************************
 * Class Ssd_74HC595_SPI
 ************************************************************************/
Ssd_74HC595_SPI::Ssd_74HC595_SPI (Spi & _spi, IOPin & _pinCs, bool _inverse):
    spi(_spi),
    pinCs(_pinCs),
    inverse(_inverse)

{
    // empty
}


void Ssd_74HC595_SPI::putString (const char * str, const bool * dots, uint16_t segNumbers)
{
    if (segNumbers >= SEG_NUMBER)
    {
        return;
    }
    for (int i = 0; i < segNumbers; ++i)
    {
        bool d = dots == NULL? false : dots[segNumbers - 1 - i];
        segData[i] = getBits(str[segNumbers - 1 - i], d);
        if (inverse)
        {
            segData[i] = ~segData[i];
        }
    }
    pinCs.setLow();
    spi.transmitDma(this, &segData[0], segNumbers);
}


void Ssd_74HC595_SPI::putDots (const bool * dots, uint16_t segNumbers)
{
    if (segNumbers >= SEG_NUMBER)
    {
        return;
    }
    for (int i = 0; i < segNumbers; ++i)
    {
        bool d = inverse? !dots[segNumbers - 1 - i] : dots[segNumbers - 1 - i];
        if (d)
        {
            setBitToTrue(segData[i], sm.dot);
        }
        else
        {
            setBitToFalse(segData[i], sm.dot);
        }
    }
    pinCs.setLow();
    spi.transmitDma(this, &segData[0], segNumbers);
}


bool Ssd_74HC595_SPI::onTransmissionFinished ()
{
    while (spi.isBusy());
    pinCs.setHigh();
    return true;
}
